pumpkins628/Light-for-You/PCB/1.png

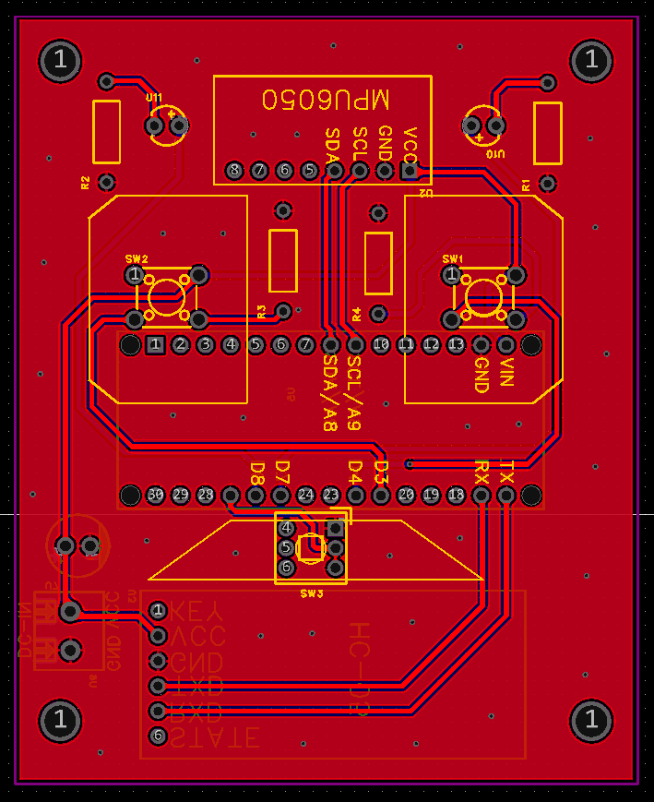
PCB/1.png
