pumpkins628/Light-for-You/PCB/2.png

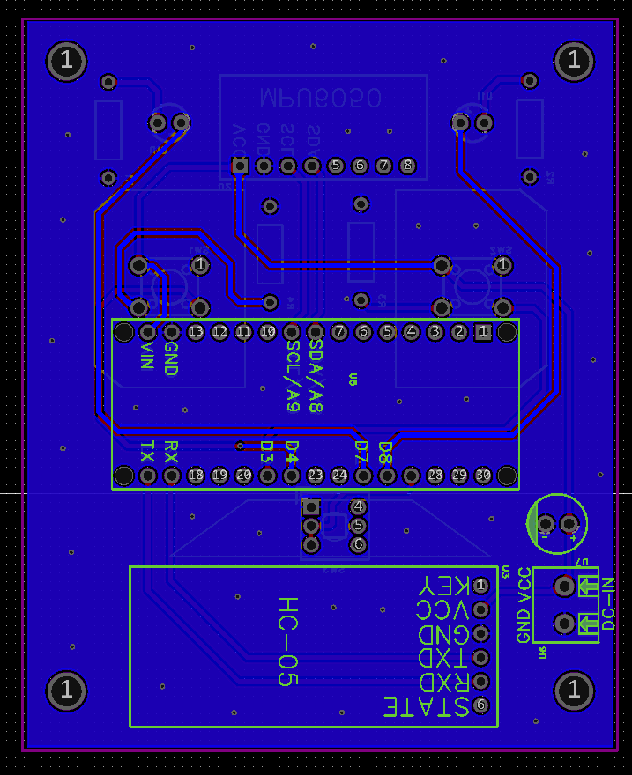
PCB/2.png
