pumpkins628/Light-for-You/PCB/3.png

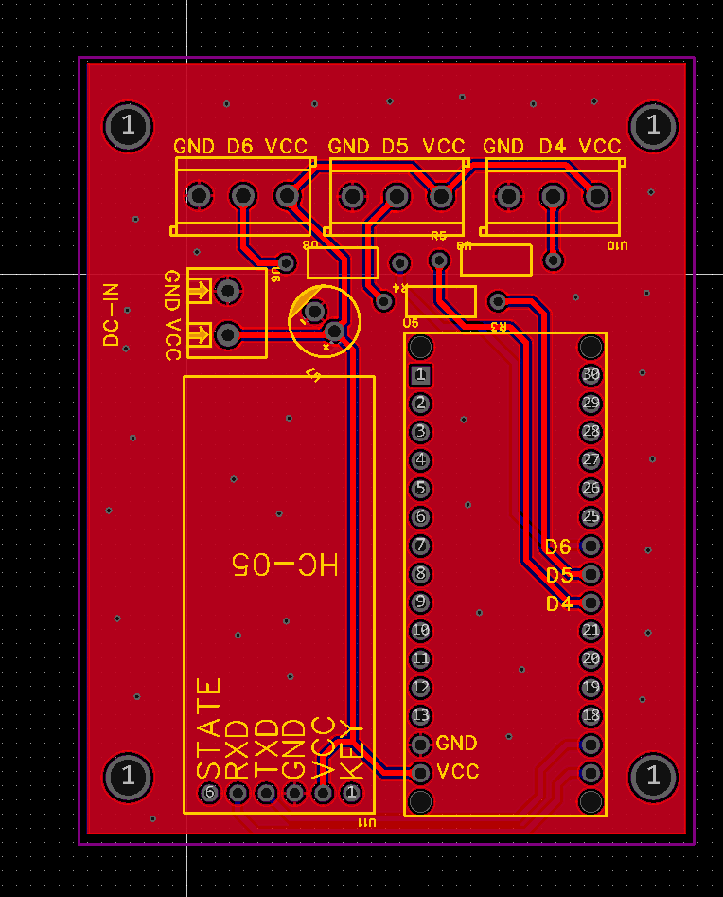
PCB/3.png
