pumpkins628/Light-for-You/PCB/4.png

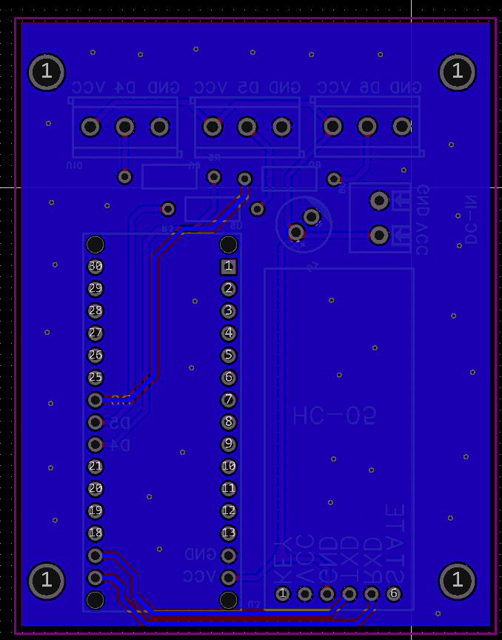
PCB/4.png
